peng-zhihui/HoloCubic/2.Firmware/HoloCubic-fw/include/network.h

#ifndef NETWORK_H
#define NETWORK_H

#include <WiFi.h>
#include <HTTPClient.h>

 
class Network
{
private:
	 
public:
	void init(String ssid, String password);
	unsigned int getBilibiliFans(String url);

};

#endif
