peng-zhihui/HoloCubic/2.Firmware/HoloCubic-fw/include/display.h

#ifndef DISPLAY_H
#define DISPLAY_H

#include <lvgl.h>

#define LCD_BL_PIN 5
#define LCD_BL_PWM_CHANNEL 0


class Display
{
private:


public:
	void init();
	void routine();
	void setBackLight(float);
};

#endif
