peng-zhihui/HoloCubic/3.Software/LvglSimulator/vs2019_proj/lvgl_similator.cpp

/**
* @file main
*
*/

/*********************
*      INCLUDES
*********************/
#include <stdlib.h>
#include <Windows.h>
#include <SDL.h>
#include "lvgl/lvgl.h"
#include "lv_drivers/display/monitor.h"
#include "lv_drivers/indev/mouse.h"
#include "lv_drivers/indev/keyboard.h"

#include "lv_examples/lv_examples.h"
#include "lv_cubic_gui.h"
/*********************
*      DEFINES
*********************/

/**********************
*      TYPEDEFS
**********************/

/**********************
*  STATIC PROTOTYPES
**********************/
static void hal_init(void);
static int tick_thread(void* data);

/**********************
*  STATIC VARIABLES
**********************/
static lv_indev_t* kb_indev;

/**********************
*      MACROS
**********************/

/**********************
*   GLOBAL FUNCTIONS
**********************/


int main(int argc, char** argv)
{
	/*Initialize LittlevGL*/
	lv_init();

	/*Initialize the HAL for LittlevGL*/
	hal_init();

	/*
	 * Demos, benchmarks, and tests.
	 *
	 * Uncomment any one (and only one) of the functions below to run that
	 * item.
	 */

	 //lv_demo_widgets();
	 //lv_demo_benchmark();
	 lv_demo_keypad_encoder();
	 //lv_demo_printer();
	 //lv_demo_stress();
	 //lv_ex_get_started_1();
	 //lv_ex_get_started_2();
	 //lv_ex_get_started_3();

	 //lv_ex_style_1();
	 //lv_ex_style_2();
	 //lv_ex_style_3();
	 //lv_ex_style_4();
	 //lv_ex_style_5();
	 //lv_ex_style_6();
	 //lv_ex_style_7();
	 //lv_ex_style_8();
	 //lv_ex_style_9();
	 //lv_ex_style_10();
	 //lv_ex_style_11();

	 /*
	  * There are many examples of individual widgets found under the
	  * lv_examples/src/lv_ex_widgets directory.  Here are a few sample test
	  * functions.  Look in that directory to find all the rest.
	  */
	  //lv_ex_arc_1();
	  //lv_ex_cpicker_1();
	  //lv_ex_gauge_1();
	  //lv_ex_img_1();
	  //lv_ex_tileview_1();

	//lv_holo_cubic_gui();

	//lv_scr_load_anim(scr_2, LV_SCR_LOAD_ANIM_OVER_BOTTOM, 300, 5000, false);


	while (1)
	{
		/* Periodically call the lv_task handler.
		* It could be done in a timer interrupt or an OS task too.*/
		lv_task_handler();
		Sleep(10);       /*Just to let the system breathe */
	}

	return 0;
}

/**********************
*   STATIC FUNCTIONS
**********************/


/**
* Initialize the Hardware Abstraction Layer (HAL) for the Littlev graphics library
*/
static void hal_init(void)
{
	/* Add a display
	* Use the 'monitor' driver which creates window on PC's monitor to simulate a display*/
	monitor_init();

	lv_disp_drv_t disp_drv;
	lv_disp_drv_init(&disp_drv);            /*Basic initialization*/

	static lv_disp_buf_t disp_buf1;
	static lv_color_t buf1_1[LV_HOR_RES_MAX * LV_VER_RES_MAX];
	lv_disp_buf_init(&disp_buf1, buf1_1, NULL, LV_HOR_RES_MAX * LV_VER_RES_MAX);

	disp_drv.buffer = &disp_buf1;
	disp_drv.flush_cb = monitor_flush;
	lv_disp_drv_register(&disp_drv);

	/* Add the mouse (or touchpad) as input device
	* Use the 'mouse' driver which reads the PC's mouse*/
	mouse_init();
	lv_indev_drv_t indev_drv;
	lv_indev_drv_init(&indev_drv);          /*Basic initialization*/
	indev_drv.type = LV_INDEV_TYPE_POINTER;
	indev_drv.read_cb = mouse_read;         /*This function will be called periodically (by the library) to get the mouse position and state*/
	lv_indev_drv_register(&indev_drv);

	/* If the PC keyboard driver is enabled in`lv_drv_conf.h`
	* add this as an input device. It might be used in some examples. */
#if USE_KEYBOARD
	lv_indev_drv_t kb_drv;
	lv_indev_drv_init(&kb_drv);
	kb_drv.type = LV_INDEV_TYPE_KEYPAD;
	kb_drv.read_cb = keyboard_read;
	kb_indev = lv_indev_drv_register(&kb_drv);
#endif

	/* Tick init.
	* You have to call 'lv_tick_inc()' in every milliseconds
	* Create an SDL thread to do this*/
	SDL_CreateThread(tick_thread, "tick", NULL);
}

/**
* A task to measure the elapsed time for LittlevGL
* @param data unused
* @return never return
*/
static int tick_thread(void* data)
{
	while (1)
	{
		lv_tick_inc(5);
		SDL_Delay(5);   /*Sleep for 5 millisecond*/
	}

	return 0;
}
