peng-zhihui/HoloCubic/3.Software/LvglSimulator/vs2019_proj/images.h

#ifndef IMAGES_H
#define IMAGES_H

#include "lvgl/lvgl.h"

#ifndef LV_ATTRIBUTE_MEM_ALIGN
#define LV_ATTRIBUTE_MEM_ALIGN
#endif

const LV_ATTRIBUTE_MEM_ALIGN LV_ATTRIBUTE_LARGE_CONST   uint8_t ali_map[] = {
  0x1c, 0x1e, 0x10, 0xff, 	/*Color of index 0*/
  0x89, 0x8f, 0x7e, 0xff, 	/*Color of index 1*/
  0x0b, 0x1b, 0xa4, 0xff, 	/*Color of index 2*/
  0x34, 0x92, 0xe9, 0xff, 	/*Color of index 3*/
  0x80, 0xd1, 0xf4, 0xff, 	/*Color of index 4*/
  0x27, 0x57, 0xa4, 0xff, 	/*Color of index 5*/
  0x90, 0xb5, 0xd7, 0xff, 	/*Color of index 6*/
  0x1d, 0x67, 0xdf, 0xff, 	/*Color of index 7*/
  0x50, 0xb2, 0xef, 0xff, 	/*Color of index 8*/
  0x5f, 0x57, 0x28, 0xff, 	/*Color of index 9*/
  0x3c, 0x52, 0x58, 0xff, 	/*Color of index 10*/
  0xb5, 0xde, 0xf5, 0xff, 	/*Color of index 11*/
  0x0a, 0x19, 0x6e, 0xff, 	/*Color of index 12*/
  0xbf, 0xb0, 0x92, 0xff, 	/*Color of index 13*/
  0x07, 0x0c, 0xdd, 0xff, 	/*Color of index 14*/
  0x6f, 0x70, 0x5c, 0xff, 	/*Color of index 15*/

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
};
const lv_img_dsc_t cat = {
  .header.always_zero = 0,
  .header.w = 240,
  .header.h = 240,
  .data_size = 28864,
  .header.cf = LV_IMG_CF_INDEXED_4BIT,
  .data = cat_map,
};

#endif
