peng-zhihui/HoloCubic/3.Software/LvglSimulator/vs2019_proj/lv_cubic_gui.c

/*********************
 *      INCLUDES
 *********************/
#include "lv_cubic_gui.h"
#include "images.h"
#include <stdlib.h>

lv_obj_t* scr_1;
lv_obj_t* scr_2;


void lv_holo_cubic_gui(void)
{
	static lv_style_t default_style;
	lv_style_init(&default_style);
	lv_style_set_bg_color(&default_style, LV_STATE_DEFAULT, LV_COLOR_BLACK);
	lv_style_set_bg_color(&default_style, LV_STATE_PRESSED, LV_COLOR_GRAY);
	lv_style_set_bg_color(&default_style, LV_STATE_FOCUSED, LV_COLOR_BLACK);
	lv_style_set_bg_color(&default_style, LV_STATE_FOCUSED | LV_STATE_PRESSED, lv_color_hex(0xf88));

	lv_obj_add_style(lv_scr_act(), LV_BTN_PART_MAIN, &default_style);

	scr_1 = lv_scr_act();
	lv_obj_t* img1 = lv_img_create(scr_1, NULL);
	lv_img_set_src(img1, &ali);
	lv_obj_align(img1, NULL, LV_ALIGN_CENTER, 0, 0);

	scr_2 = lv_obj_create(NULL, NULL);
	lv_obj_t* img2 = lv_img_create(scr_2, NULL);
	lv_img_set_src(img2, &cat);
	lv_obj_align(img2, NULL, LV_ALIGN_CENTER, 0, 0);

	lv_obj_t* label1 = lv_label_create(scr_1, NULL);
 
	lv_label_set_text_fmt(label1, "CPU Temp: %d C", 0);
	lv_obj_set_pos(label1, 20, 30);
}
