peng-zhihui/HoloCubic/3.Software/LvglSimulator/vs2019_proj/lv_drivers/indev/FT5406EE8.h

/**
 * @file FT5406EE8.h
 *
 */

#ifndef FT5406EE8_H
#define FT5406EE8_H

#ifdef __cplusplus
extern "C" {
#endif

/*********************
 *      INCLUDES
 *********************/
#ifndef LV_DRV_NO_CONF
#ifdef LV_CONF_INCLUDE_SIMPLE
#include "lv_drv_conf.h"
#else
#include "../../lv_drv_conf.h"
#endif
#endif

#if USE_FT5406EE8

#ifdef LV_LVGL_H_INCLUDE_SIMPLE
#include "lvgl.h"
#else
#include "lvgl/lvgl.h"
#endif

/*********************
 *      DEFINES
 *********************/

/**********************
 *      TYPEDEFS
 **********************/

/**********************
 * GLOBAL PROTOTYPES
 **********************/
void ft5406ee8_init(void);
bool ft5406ee8_read(lv_indev_drv_t * indev_drv, lv_indev_data_t * data);

/**********************
 *      MACROS
 **********************/

#endif /* USE_FT5406EE8 */

#ifdef __cplusplus
} /* extern "C" */
#endif

#endif /* FT5406EE8_H */
