peng-zhihui/HoloCubic/3.Software/LvglSimulator/vs2019_proj/lv_drivers/indev/XPT2046.h

/**
 * @file XPT2046.h
 *
 */

#ifndef XPT2046_H
#define XPT2046_H

#ifdef __cplusplus
extern "C" {
#endif

/*********************
 *      INCLUDES
 *********************/
#ifndef LV_DRV_NO_CONF
#ifdef LV_CONF_INCLUDE_SIMPLE
#include "lv_drv_conf.h"
#else
#include "../../lv_drv_conf.h"
#endif
#endif

#if USE_XPT2046

#ifdef LV_LVGL_H_INCLUDE_SIMPLE
#include "lvgl.h"
#else
#include "lvgl/lvgl.h"
#endif

/*********************
 *      DEFINES
 *********************/

/**********************
 *      TYPEDEFS
 **********************/

/**********************
 * GLOBAL PROTOTYPES
 **********************/
void xpt2046_init(void);
bool xpt2046_read(lv_indev_drv_t * indev_drv, lv_indev_data_t * data);

/**********************
 *      MACROS
 **********************/

#endif /* USE_XPT2046 */

#ifdef __cplusplus
} /* extern "C" */
#endif

#endif /* XPT2046_H */
